Maniak003/AlphaSpectrometr/Documents/AM-D1-10112024-12_5.png

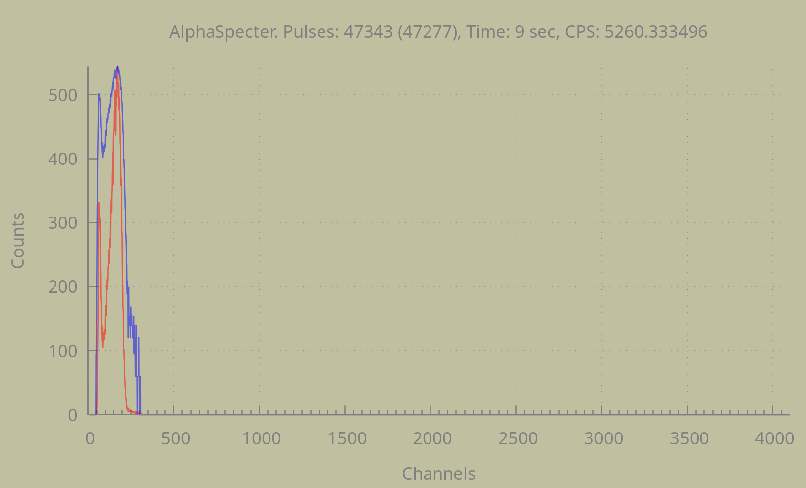
Documents/AM-D1-10112024-12_5.png
