Maniak003/AlphaSpectrometr/Documents/AM-D1-10112024-47_5-10M.png

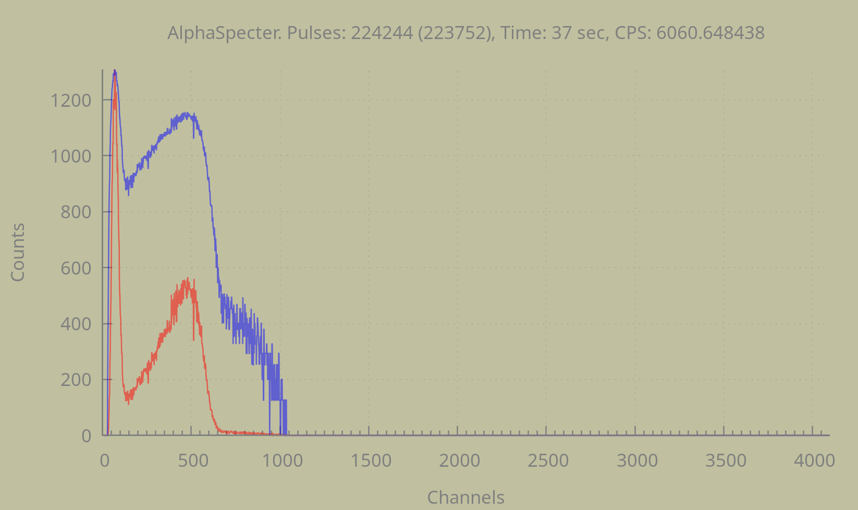
Documents/AM-D1-10112024-47_5-10M.png
