Maniak003/AlphaSpectrometr/Documents/AM-D1-10112024-92_5-10M.png

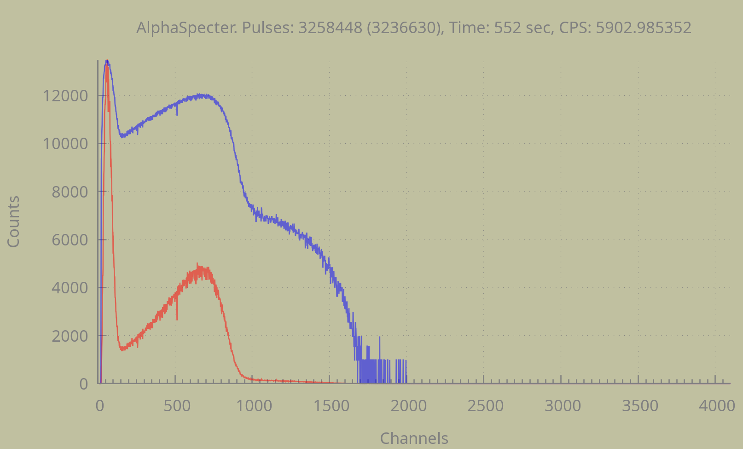
Documents/AM-D1-10112024-92_5-10M.png
