Maniak003/AlphaSpectrometr/Documents/AM-D1.png

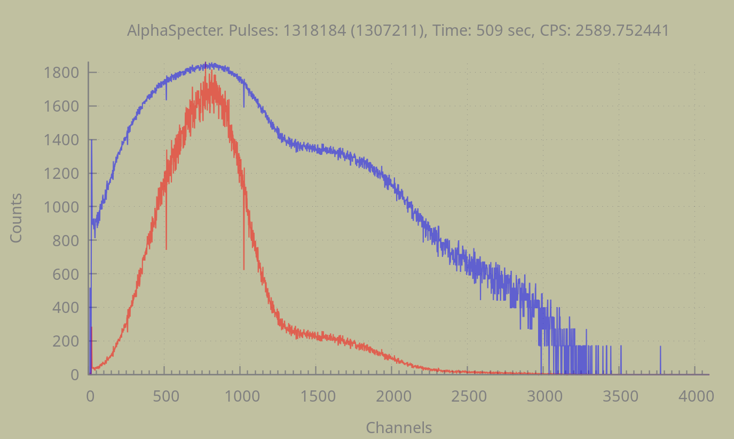
Documents/AM-D1.png
