Maniak003/AlphaSpectrometr/Documents/AM-D2.png

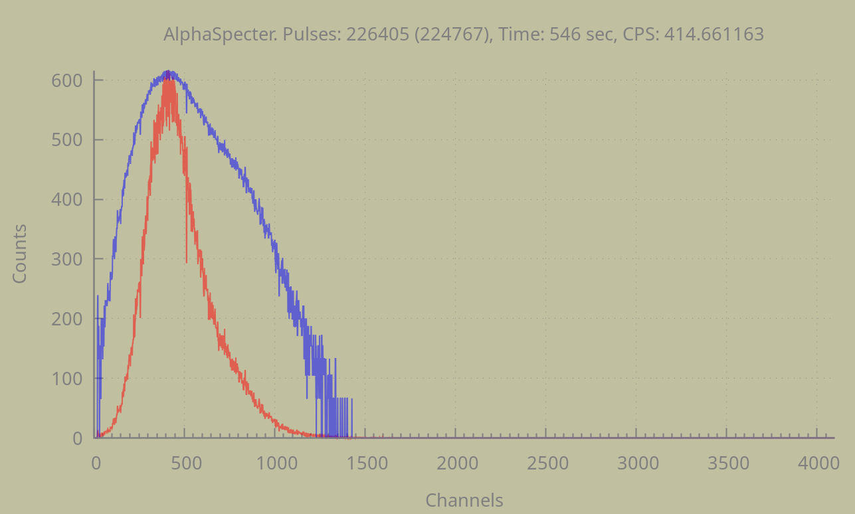
Documents/AM-D2.png
