Maniak003/AlphaSpectrometr/Documents/AM-D3.png

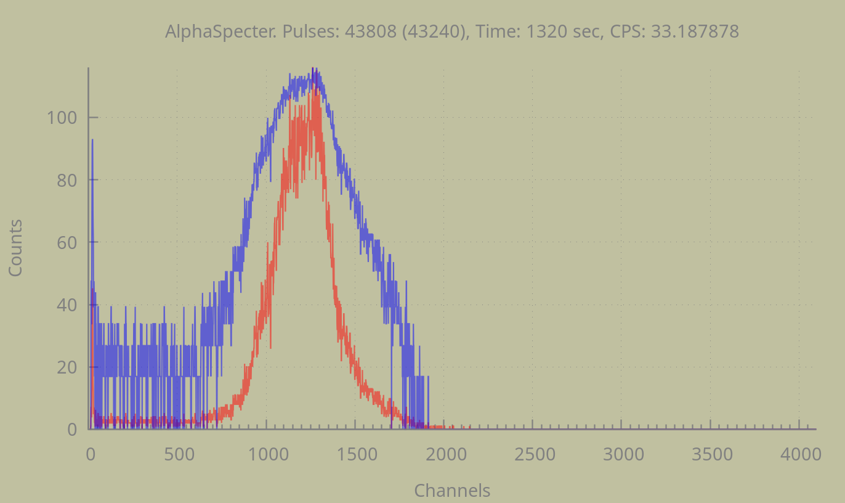
Documents/AM-D3.png
