Maniak003/AlphaSpectrometr/Documents/AS.png

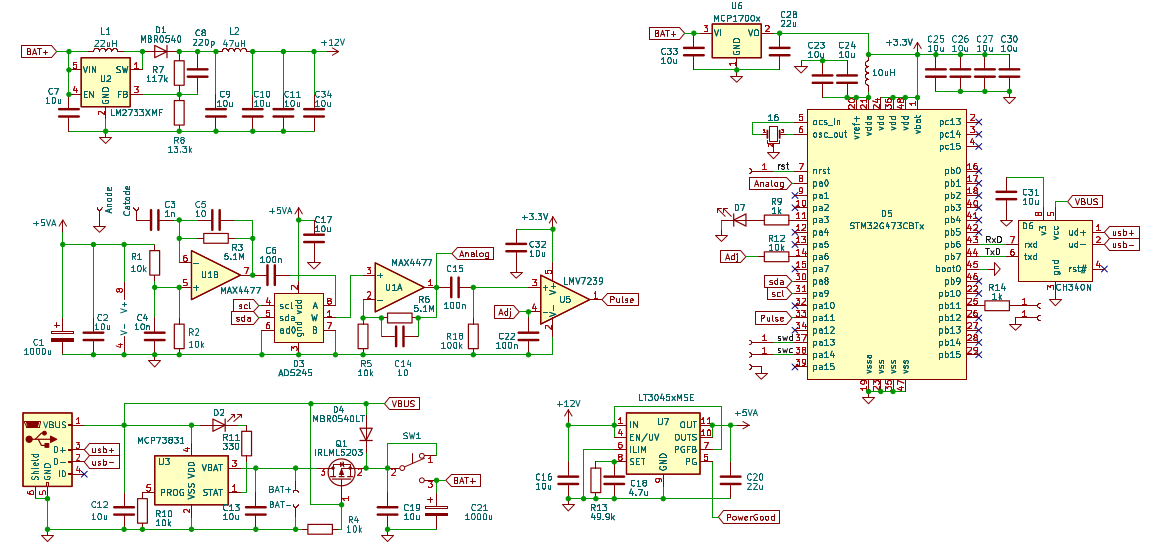
Documents/AS.png
