Maniak003/AlphaSpectrometr/Documents/RN-17112024.png

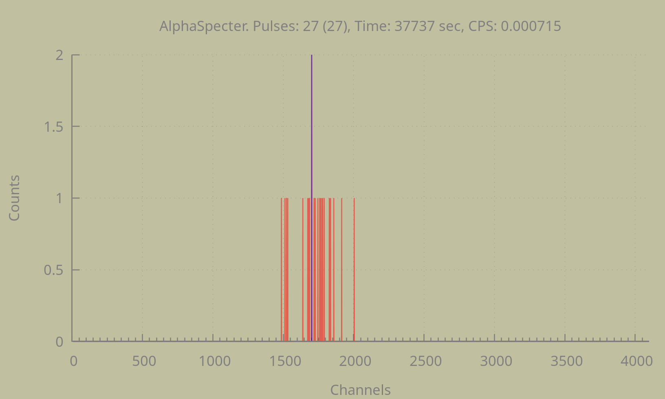
Documents/RN-17112024.png
