Maniak003/AlphaSpectrometr/Documents/RN-D1-11112024.png

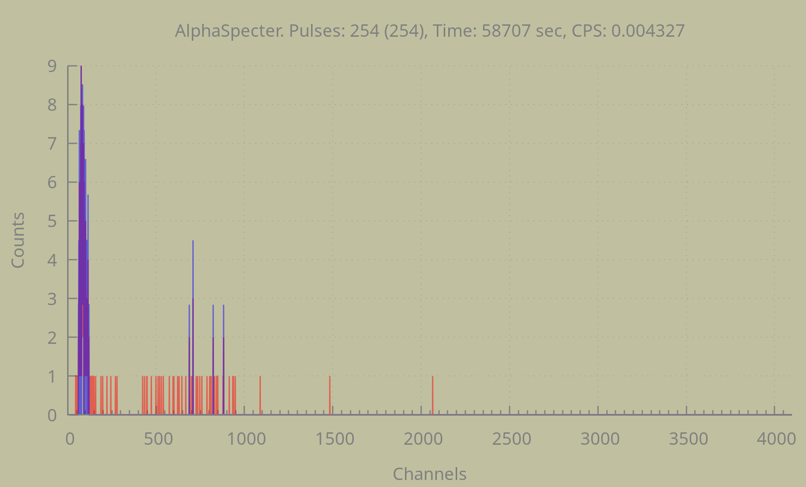
Documents/RN-D1-11112024.png
