Maniak003/AlphaSpectrometr/STM32CubeIDE/TestController/Core/Inc/main.h

#define AnalogIn_Pin GPIO_PIN_0
#define AnalogIn_GPIO_Port GPIOA
#define LED_Pin GPIO_PIN_3
#define LED_GPIO_Port GPIOA
#define AdjHV_Pin GPIO_PIN_4
#define AdjHV_GPIO_Port GPIOA
#define Comp_level_Pin GPIO_PIN_6
#define Comp_level_GPIO_Port GPIOA
#define PULSE_CLIBRATE_Pin GPIO_PIN_11
#define PULSE_CLIBRATE_GPIO_Port GPIOB
#define ADCsync_Pin GPIO_PIN_11
#define ADCsync_GPIO_Port GPIOA
#define SWD_Pin GPIO_PIN_13
#define SWD_GPIO_Port GPIOA
#define SWC_Pin GPIO_PIN_14
#define SWC_GPIO_Port GPIOA
#define TX_Pin GPIO_PIN_6
#define TX_GPIO_Port GPIOB
#define RX_Pin GPIO_PIN_7
#define RX_GPIO_Port GPIOB
#define SPECTER_SIZE 4096
